wflosin/Digital-Audio-Interface-V1/AudioEQfromGuitar_sims.asc

C1: cap; 120p
C2: cap; 500p
C3: polcap; 22µ
C4: polcap; 15µ
C5: cap; 4.7n
C6: cap; 22n
C7: cap; 47n
C8: cap; 1.2n
C10: cap; 4.7n
C12: polcap; 22µ
C16: cap; 100p
D1: LED; PT-121-B
L1: ind; 2.2
R1: res; 5.8k
R2: res; 250k
R3: res; 250k
R4: res; 1Meg
R5: res; 22k
R6: res; 3.3k
R7: res; {1m+MID*100k}
R8: res; {1m+(1-MID)*100k}
R9: res; 3.3k
R10: res; 10k
R11: res; {1m+BASS*100k}
R12: res; {1m+(1-BASS)*100k}
R13: res; 10k
R14: res; {1m+TREBLE*470k}
R15: res; {1m+(1-TREBLE)*470k}
R16: res; 1.8k
R17: res; 1.8k
R18: res; 10k
R19: res; 270
R20: res; 160
R21: res; 1
R22: res; 22k
R23: res; 22k
R24: res; {1+(1-VOL)*10k}
R25: res; {1+VOL*10k}
R26: res; 1
R27: res; 500
R28: res; 5k
R33: res; 22k
U1: OPA1622
U2: OPA1622
U3: TL331
U4: OPA1622
U5: OPA1622
V1: voltage; SINE(0 -0.4 200); AC 0.4
V2: voltage; 3.8
V3: voltage; 1.53
V4: voltage; 0.91
V5: voltage; 3.8
Named nets: 0, Guitar, 12V, VOUT, S1, S2
;ac oct 100 1 20000
.param BASS=0.5 MID=0.5 TREBLE=0.5 VOL=0.92 TEST=1
;.step param TEST list 8u 10u 15u
Guitar Pickup Simulation
Input Hi-Z Buffer
Tone Control, EQ
Baxandall Active Volume Control
.tran 5m
;noise V(VOUT) V1 oct 100 1 20000
;.step param BASS 0 1 0.25
LED clipping comparator
VCC-1.5 max
